hixfield/HixButton/hardware/images/case_3d.jpg

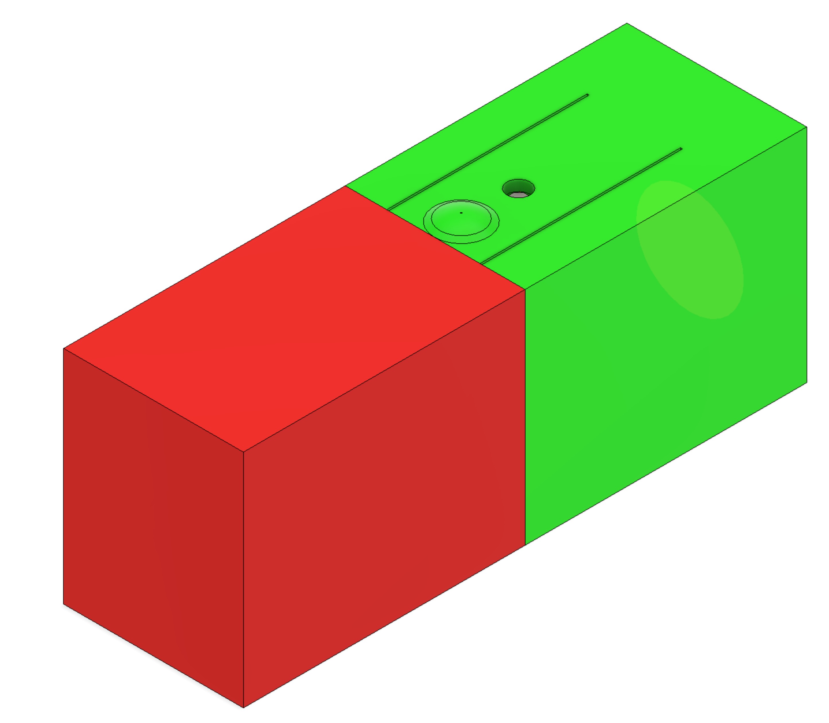
hardware/images/case_3d.jpg
