hixfield/HixButton/software/src/secret.cpp

#include "secret.h"

/*

//Contains the default settings used when the stored configuration is invalid.
//Like when the device is first booted.

const char *Secret::CONFIG_PWD = "xxxx";

const char *Secret::WIFI_SSID = "xxxx";
const char *Secret::WIFI_PWD = "xxxx";
const bool Secret::FIXED_IP_ENABLED = true;
const char *Secret::MY_IP = "xxx.xxx.xxx.xxx";
const char *Secret::MY_MASK = "xxx.xxx.xxx.xxx";
const char *Secret::MY_GATEWAY = "xxx.xxx.xxx.xxx";

const bool Secret::OTA_ENABLED = false; //not implemented (yet)
const char *Secret::MY_ROOM = "test_room";
const char *Secret::MY_DEVICE_TAG = "test_tag";
const char *Secret::UDP_SERVER = "xxx.xxx.xxx.xxx";
const int Secret::UDP_PORT = xxxxx;

*/
